marsairforce/traynor_yga1/ax84_preamp_mod/IMG_5209.jpg

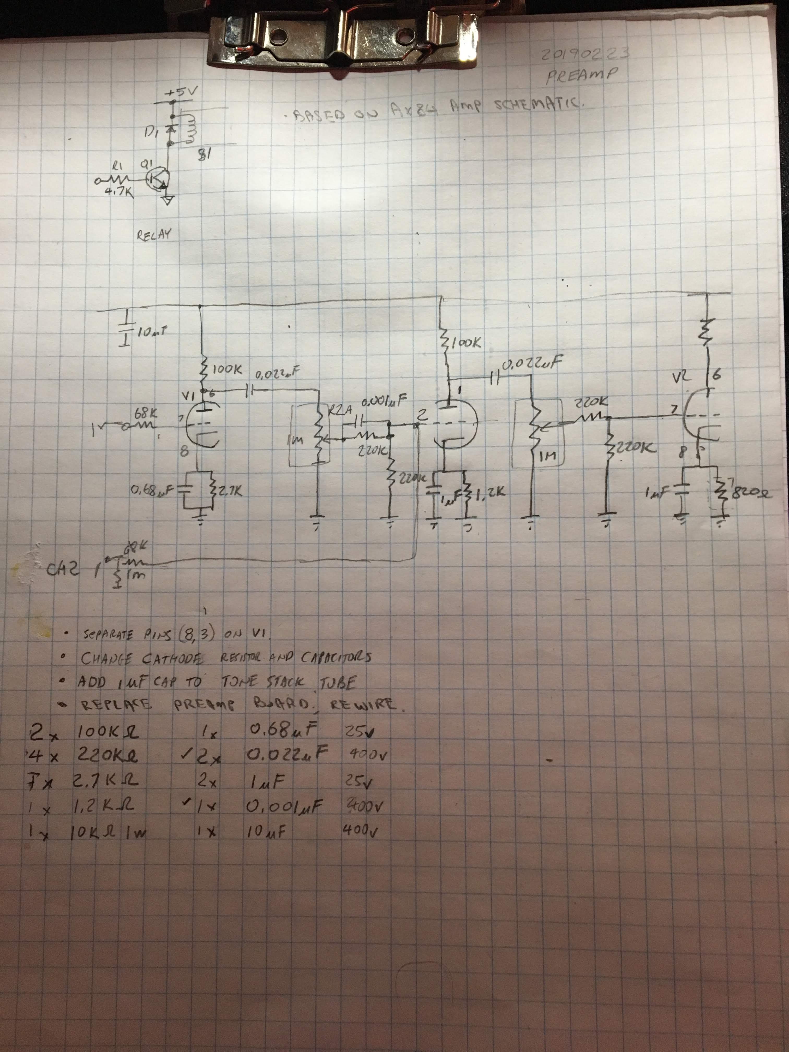
ax84_preamp_mod/IMG_5209.jpg
