marsairforce/traynor_yga1/ax84_preamp_mod/photos/IMG_5218.jpg

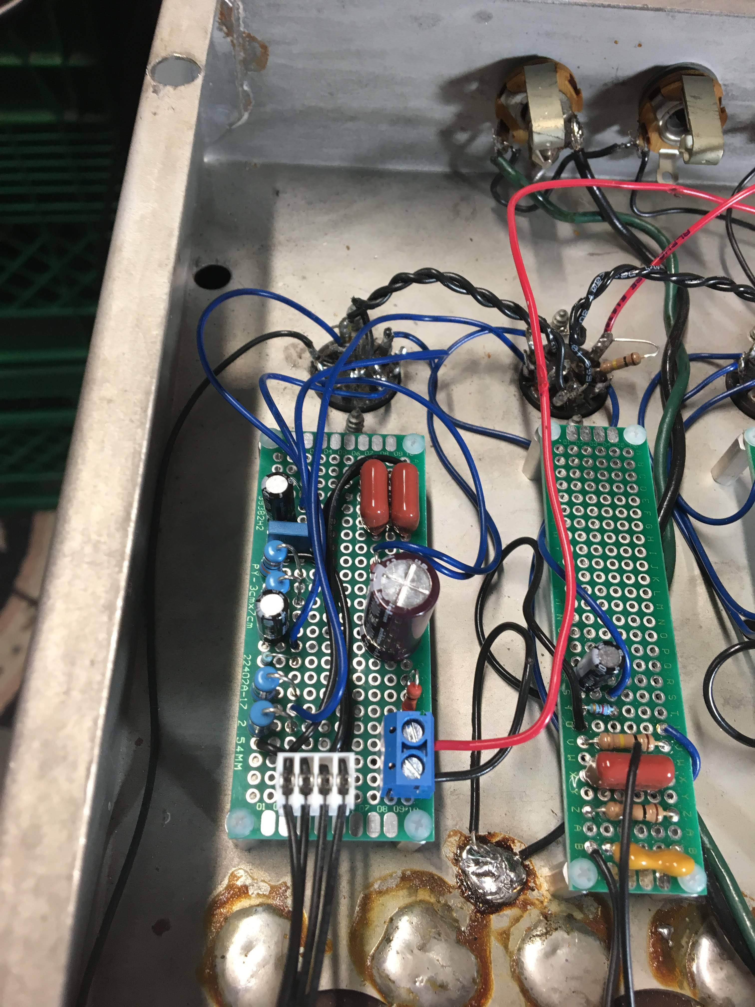
ax84_preamp_mod/photos/IMG_5218.jpg
