marsairforce/traynor_yga1/doc/IMG_4978.jpg

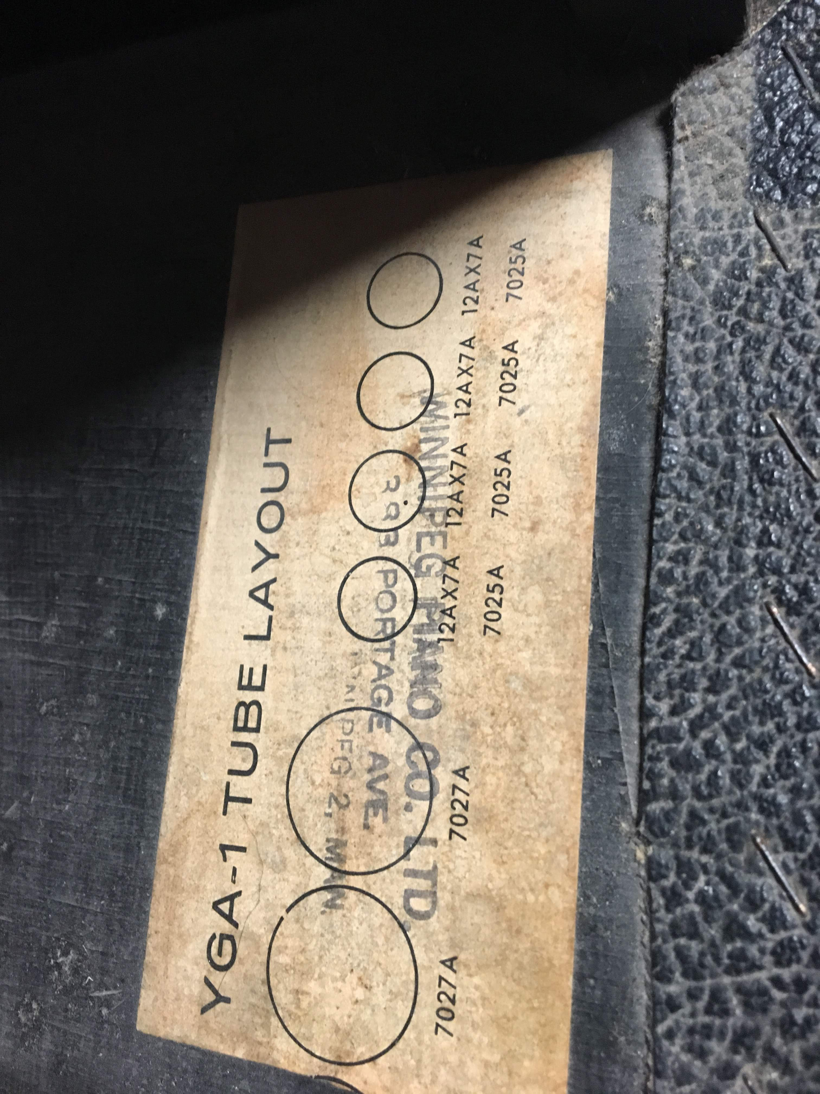
doc/IMG_4978.jpg
