marsairforce/traynor_yga1/doc/IMG_7422.jpg

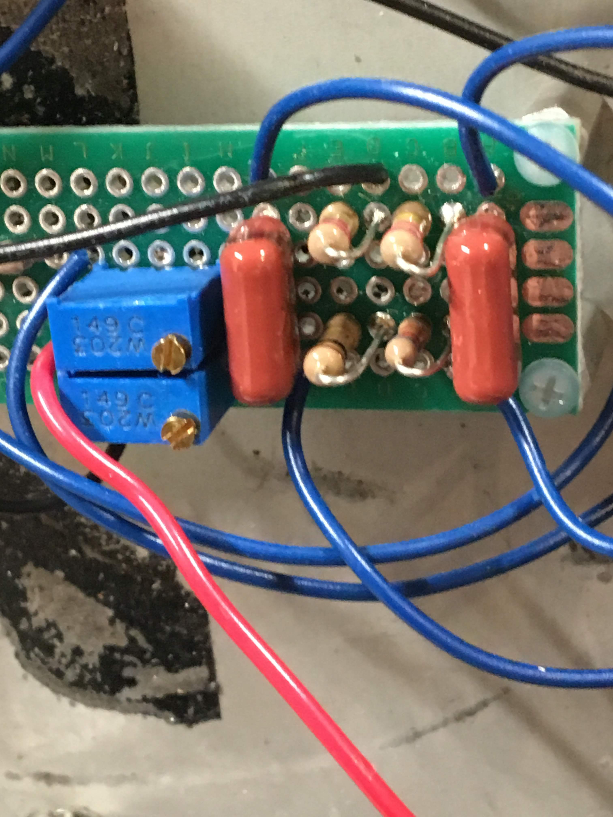
doc/IMG_7422.jpg
