marsairforce/traynor_yga1/doc/IMG_7427.JPG

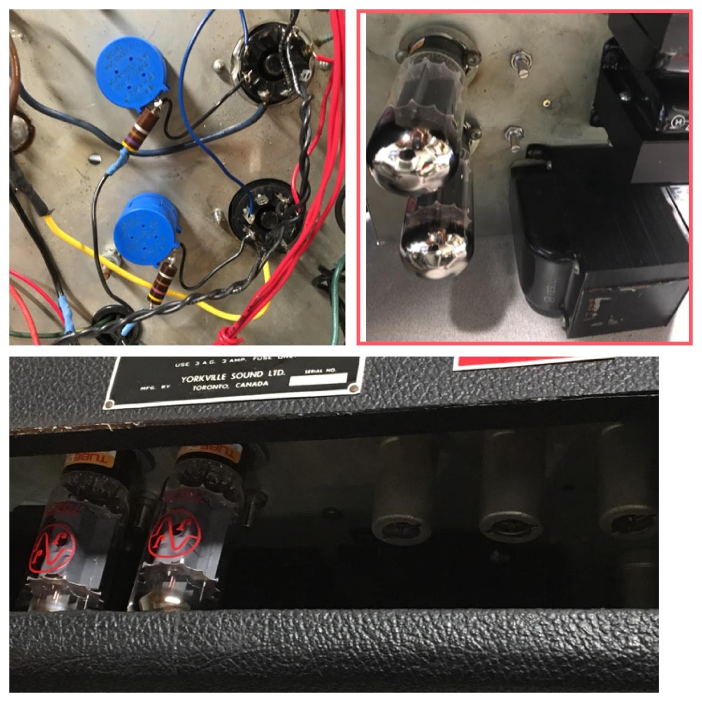
doc/IMG_7427.JPG
