marsairforce/traynor_yga1/doc/IMG_7432.JPG

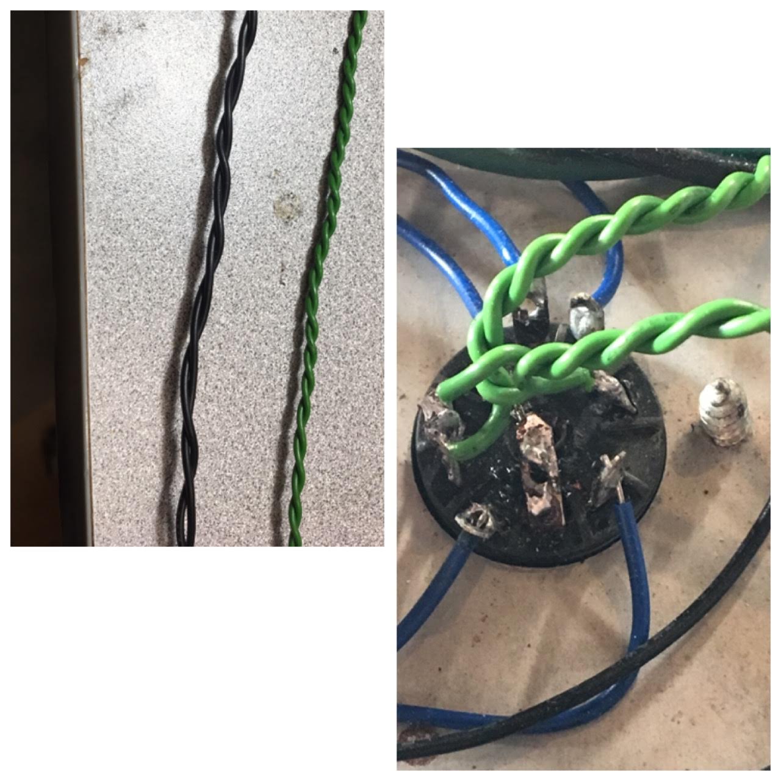
doc/IMG_7432.JPG
